banksAcc/Veesion_Cube-Tool/aruco_marker/aruco_4x4_50_75mm/aruco_4x4_50_id0_75mm.png

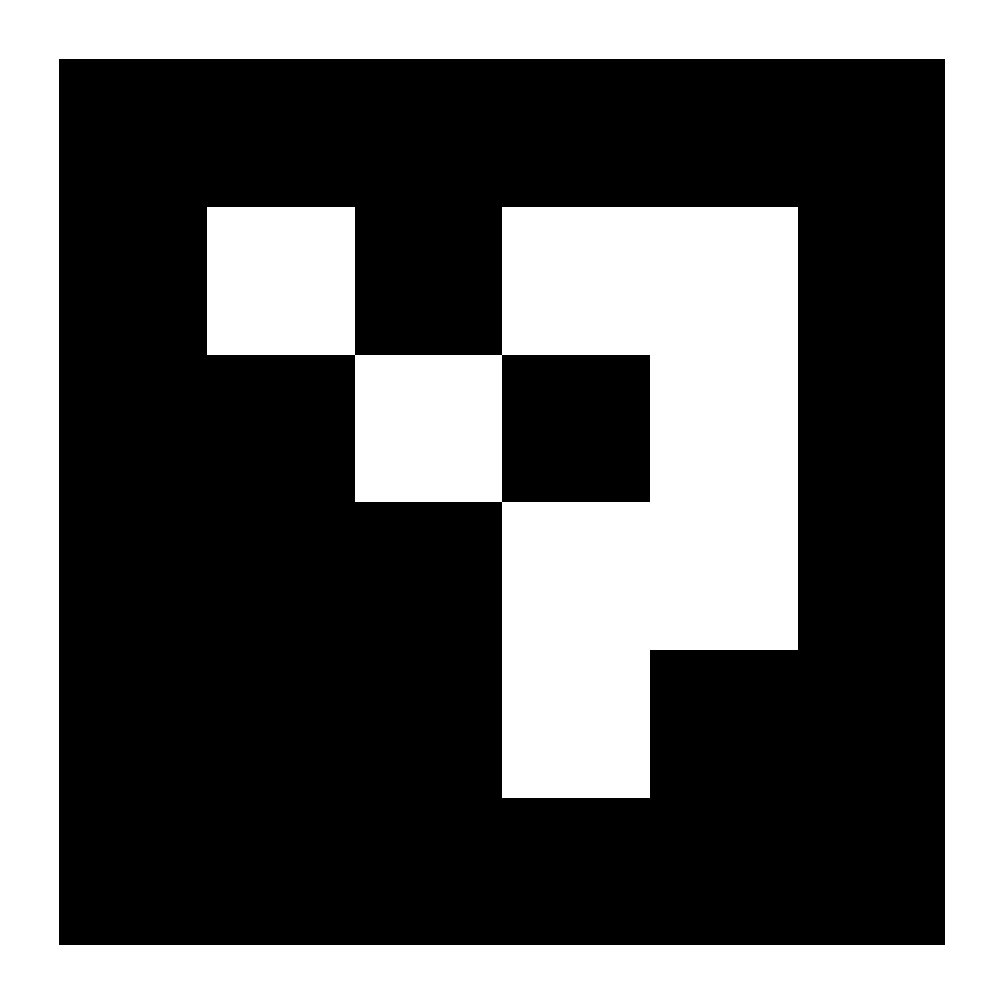
aruco_marker/aruco_4x4_50_75mm/aruco_4x4_50_id0_75mm.png
