banksAcc/Veesion_Cube-Tool/cube_minimal/data/sample_dataset/example_3.png

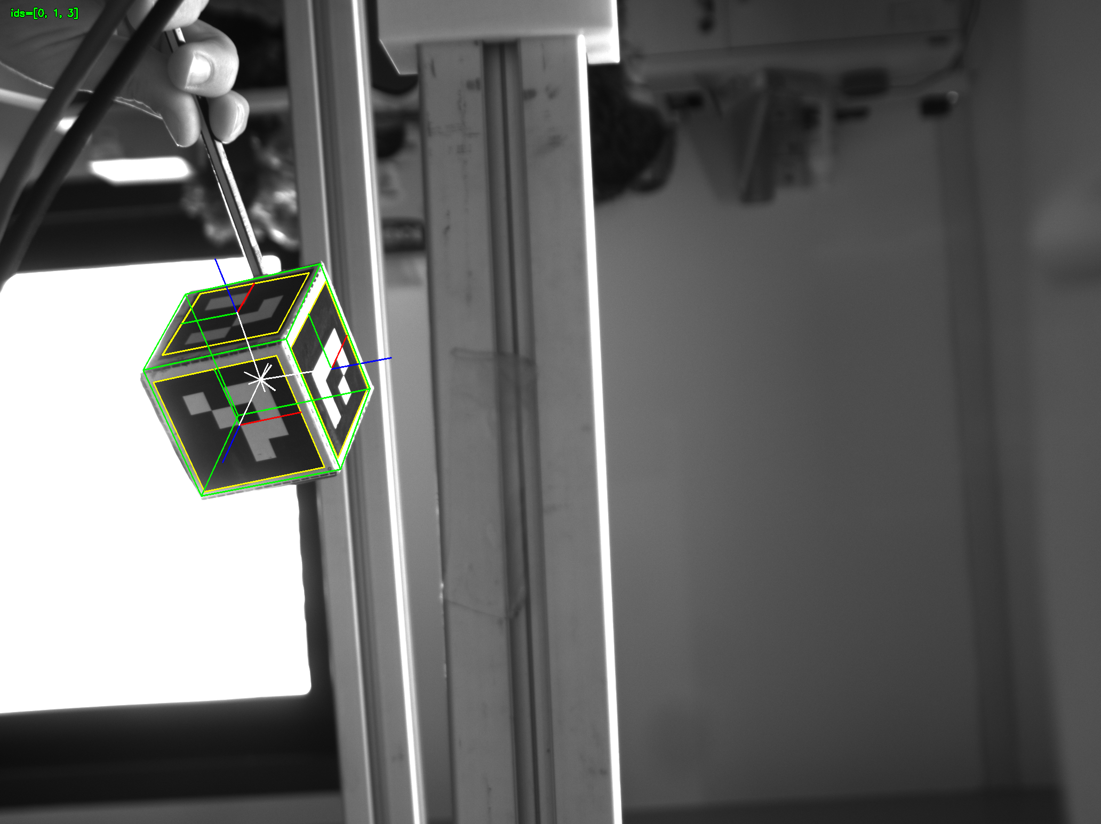
cube_minimal/data/sample_dataset/example_3.png
