banksAcc/Veesion_Cube-Tool/pc/captures/session_2025-09-25_17-20-19__2025-09-25_17-20-41/frame_000001_20250925_172019.tiff

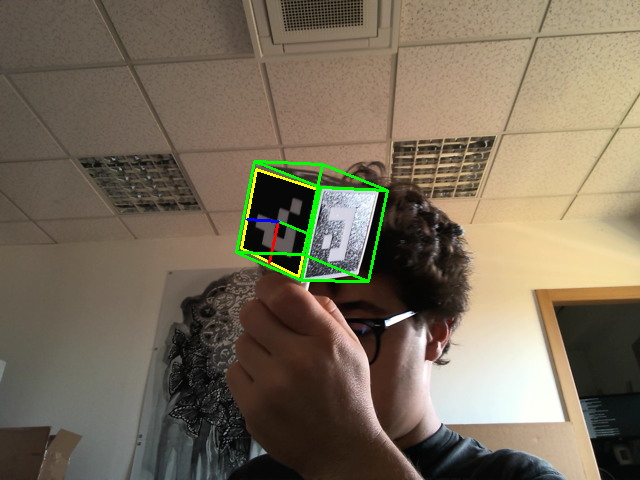
pc/captures/session_2025-09-25_17-20-19__2025-09-25_17-20-41/frame_000001_20250925_172019.tiff
