banksAcc/Veesion_Cube-Tool/pc/captures/session_2025-09-25_17-20-19__2025-09-25_17-20-41/frame_000011_20250925_172021.tiff

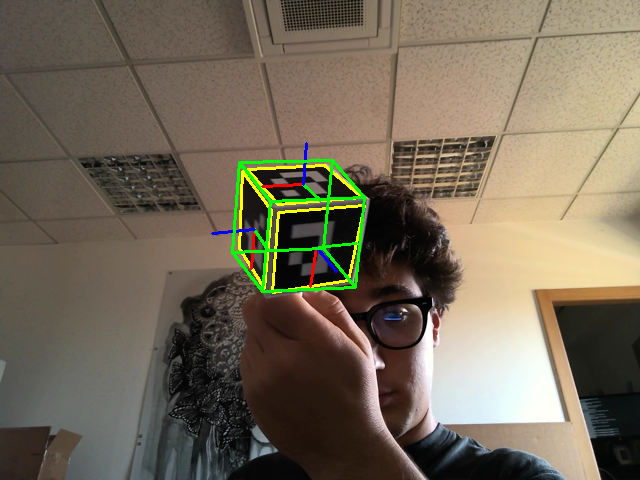
pc/captures/session_2025-09-25_17-20-19__2025-09-25_17-20-41/frame_000011_20250925_172021.tiff
