banksAcc/Veesion_Cube-Tool/pc/image_to_be_used/Basler_acA2040-35gm__23324651__20250826_151237703_0001.tiff

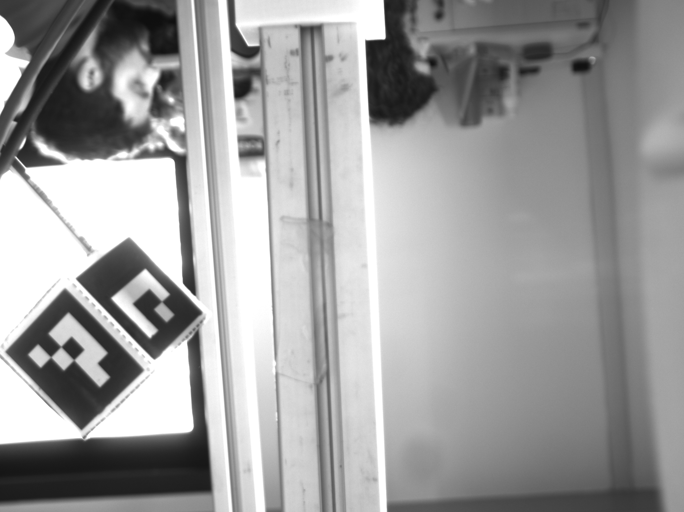
pc/image_to_be_used/Basler_acA2040-35gm__23324651__20250826_151237703_0001.tiff
